z101/x-1_led_tower/circuit/x-1_led_tower.kicad_sch

## KiCad design circuit/x-1_led_tower.kicad_sch (2024-12-09)

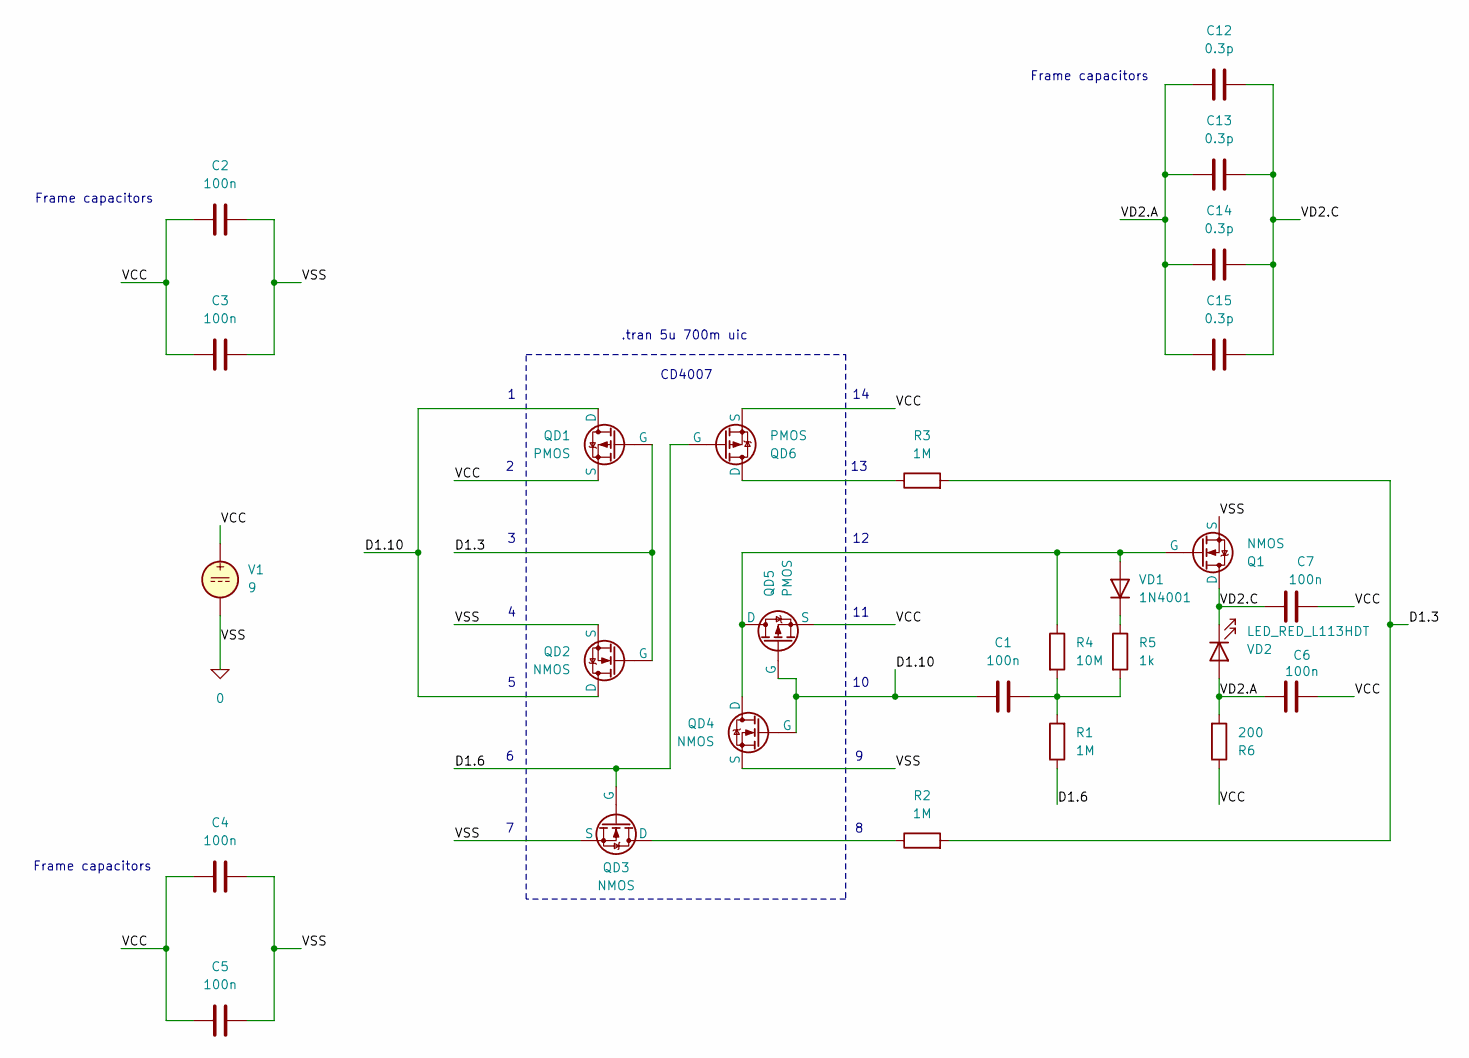
[picture p27: schematic x-1_led_tower.kicad_sch]

Parts:
C1, C2, C3, C4, C5, C6, C7: 100n
C12, C13, C14, C15: 0.3p
Q1: NMOS
QD1, QD5, QD6: PMOS
QD2, QD3, QD4: NMOS
R1, R2, R3: 1M
R4: 10M
R5: 1k
R6: 200
V1: 9
VD1: 1N4001
VD2: LED_RED_L113HDT

Connections:
0: C2.1, C3.2, C4.1, C5.2, Q1.3 (S), QD2.3 (S), QD3.3 (S), QD4.3 (S), V1.2
D1.3: QD1.2 (G), QD2.2 (G), R2.2, R3.2
D1.6: QD3.2 (G), QD6.2 (G), R1.1
D1.10: C1.1, QD1.1 (D), QD2.1 (D), QD4.2 (G), QD5.2 (G)
unnamed: C1.2, R1.2, R4.2, R5.2
unnamed: Q1.2 (G), QD4.1 (D), QD5.1 (D), R4.1, VD1.2 (A)
unnamed: QD3.1 (D), R2.1
unnamed: QD6.1 (D), R3.1
unnamed: R5.1, VD1.1 (K)
VCC: C2.2, C3.1, C4.2, C5.1, C6.2, C7.2, QD1.3 (S), QD5.3 (S), QD6.3 (S), R6.1, V1.1
VD2.A: C6.1, C12.2, C13.1, C14.1, C15.1, R6.2, VD2.2 (A)
VD2.C: C7.1, C12.1, C13.2, C14.2, C15.2, Q1.1 (D), VD2.1 (K)

Notes on the sheet:
Frame capacitors
.tran 5u 700m uic
CD4007
